jackanfossi/Chaos101/technicals/Chaos101_tech/91920A570_Female Threaded Hex Standoff.SLDPRT

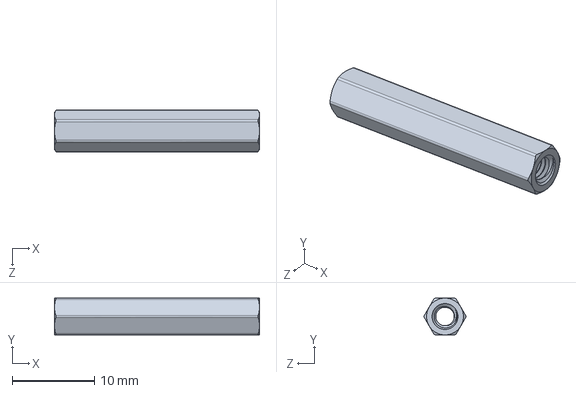
[picture p27: CAD file, 2026-05-17]
technicals/Chaos101_tech/91920A570_Female Threaded Hex Standoff.SLDPRT
25.0 x 4.50 x 5.10 mm
