jackanfossi/Chaos101/technicals/Chaos101_tech/94868A722_Female Threaded Hex Standoff(1).SLDPRT

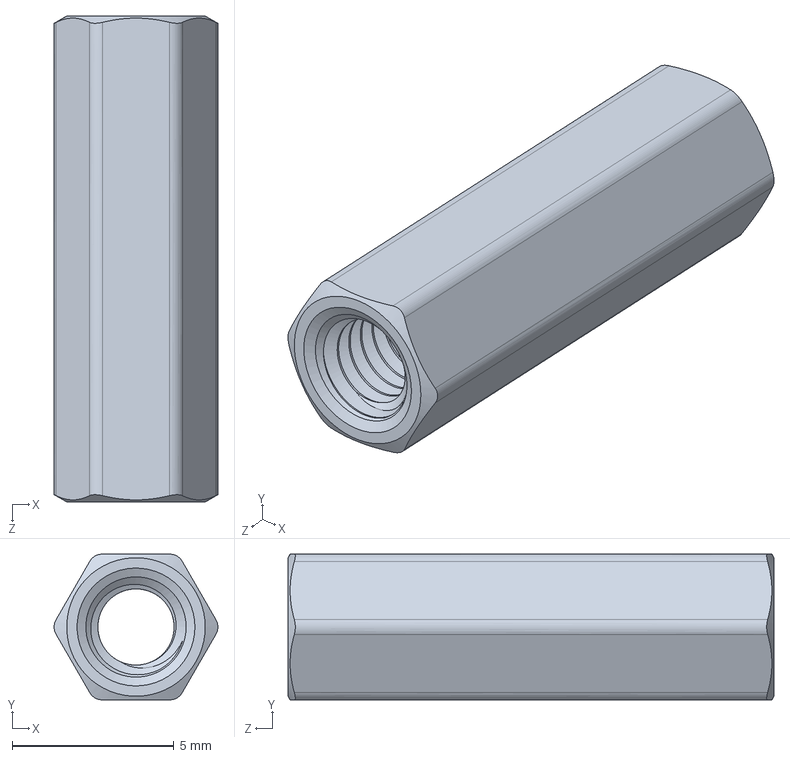
[picture p28: CAD file, 2026-05-17]
technicals/Chaos101_tech/94868A722_Female Threaded Hex Standoff(1).SLDPRT
5.06 x 4.50 x 15.0 mm
