jackanfossi/Chaos101/technicals/Chaos101_tech/Chaos101.SLDASM

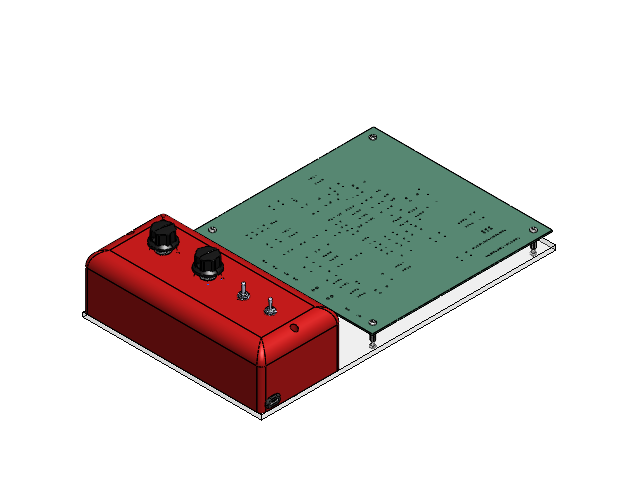
[picture p29: CAD file, 2026-05-17]
technicals/Chaos101_tech/Chaos101.SLDASM
94868A722_Female Threaded Hex Standoff(1) x 4
91200A116_18-8 Stainless Steel Pan Head Slotted Screws x 12
91920A570_Female Threaded Hex Standoff x 2
Case
Battery_Holder x 2
Plate
PCB
Washer Anti Twist Protection.step
Nut M6x0.75mm.step
Nut M6x0.75mm clone.step
Fantastic Plastic Body.step
Neck.step
Washer.step
PCB PIN 01.step
PCB PIN clone 02.step
PCB PIN clone 03.step
PCB PIN clone 04.step
PCB PIN clone 05.step
PCB PIN clone 06.step
Sheetmatal Frame.step
Font O 001.step
Font N 001.step
Font - 001.step
Font O 002.step
Font F 001.step
Font F 002.step
Font - 002.step
Font O 003.step
Font N 002.step
Batton.step
Washer Anti Twist Protection001.step
Nut M6x0.75mm 001.step
Nut M6x0.75mm clone001.step
Fantastic Plastic Body001.step
Neck001.step
Washer001.step
PCB PIN 002.step
PCB PIN clone 007.step
PCB PIN clone 008.step
Sheetmatal Frame001.step
Font O 004.step
Font N 003.step
Font - 003.step
Font O 005.step
Font F 003.step
Batton001.step
multi turn x 2
MXR_ECB130_KNOB.step x 2
9v Duracell Battery Wyatt Sanders.ipt x 2
USB-Port
